TinyCircuits/TinyCircuits-Whisker-Color-Sensor-AST1004/cad/Wireling_COLORSENSOR_AST1004_REV3-DETAILED_DRAWING-PNG.png

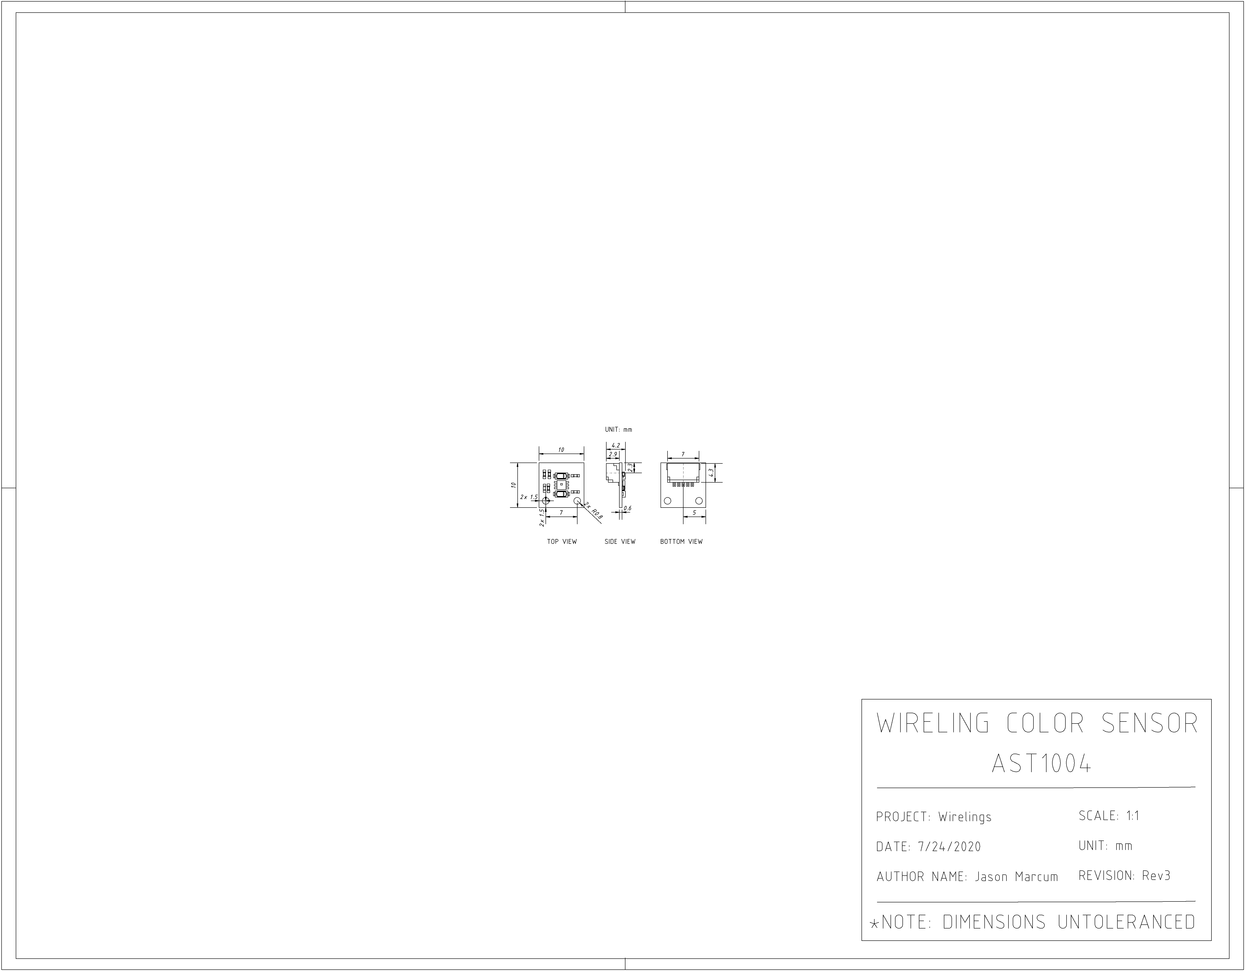
cad/Wireling_COLORSENSOR_AST1004_REV3-DETAILED_DRAWING-PNG.png
