TinyCircuits/TinyCircuits-Whisker-Color-Sensor-AST1004/images/AST1004-Tutorial-Image-03.png

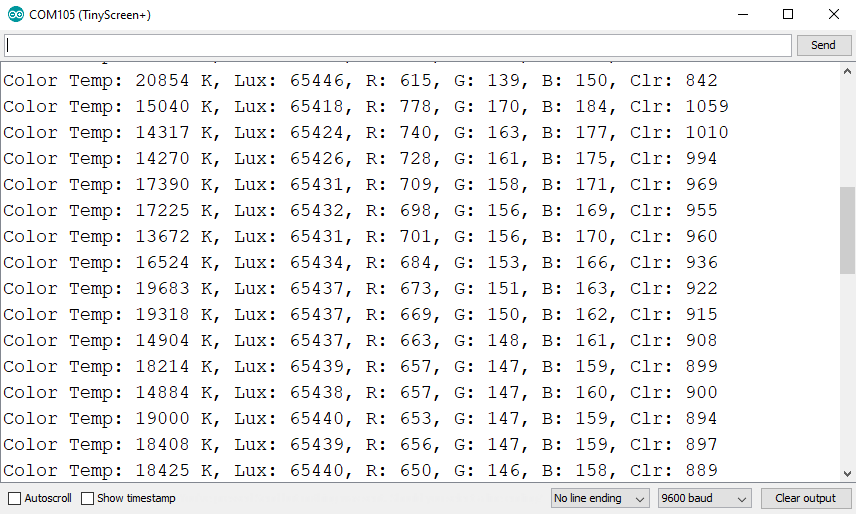
images/AST1004-Tutorial-Image-03.png
